GerardM55/TFG/Diseño mano/Archivos SLDPRT/falange proximal 4.SLDPRT

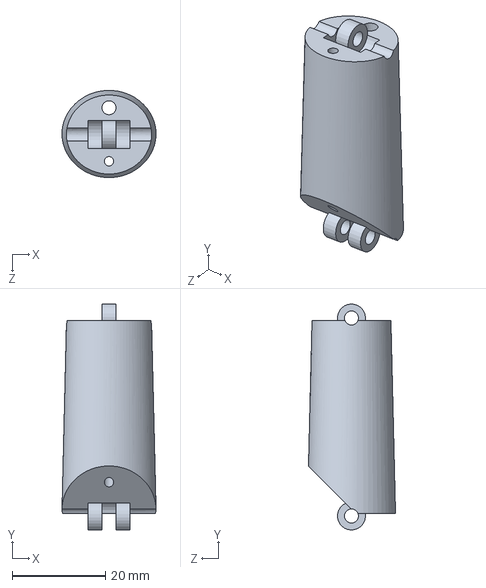
[picture p15: CAD file, 2025-07-18]
Diseño mano/Archivos SLDPRT/falange proximal 4.SLDPRT
20.2 x 48.4 x 18.6 mm
