GerardM55/TFG/Diseño mano/Archivos SLDPRT/falange proximal 3.SLDPRT

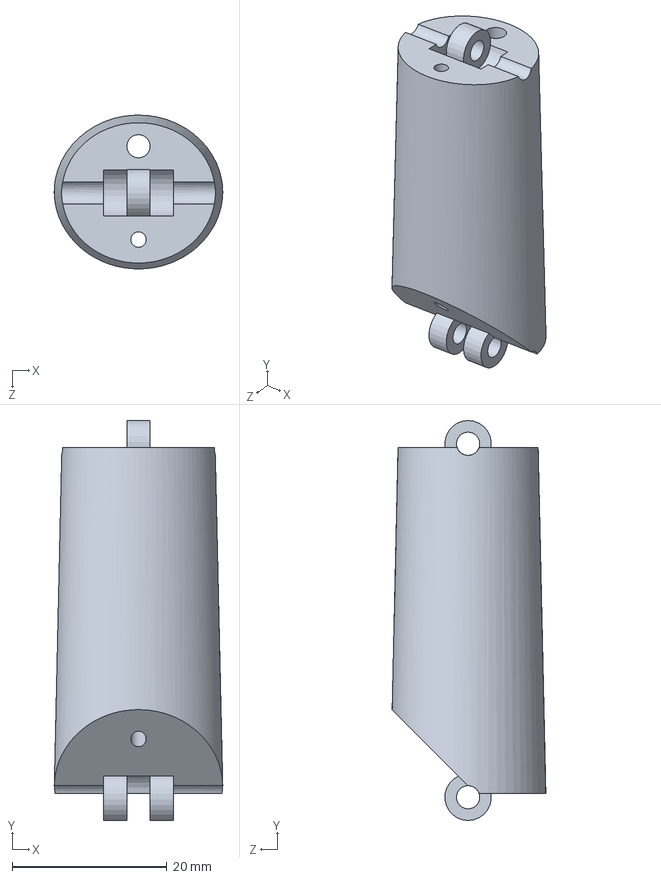
[picture p16: CAD file, 2025-07-18]
Diseño mano/Archivos SLDPRT/falange proximal 3.SLDPRT
21.8 x 51.6 x 19.9 mm
