GerardM55/TFG/Diseño mano/Archivos SLDPRT/falange proximal 2.SLDPRT

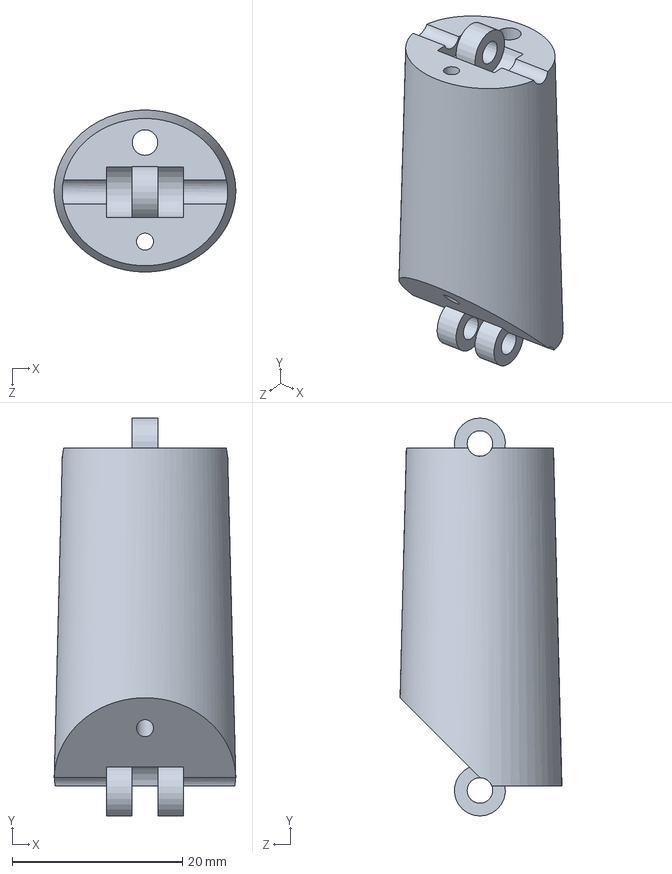
[picture p17: CAD file, 2025-07-18]
Diseño mano/Archivos SLDPRT/falange proximal 2.SLDPRT
21.3 x 46.8 x 19.0 mm
