GerardM55/TFG/Diseño mano/Archivos SLDPRT/pasador.SLDPRT

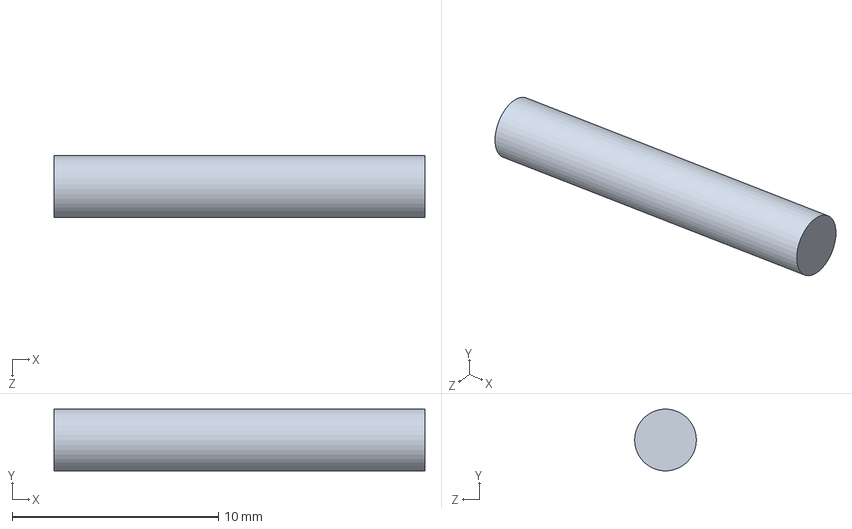
[picture p18: CAD file, 2025-07-18]
Diseño mano/Archivos SLDPRT/pasador.SLDPRT
18.0 x 2.99 x 3.00 mm
