GerardM55/TFG/Diseño mano/Archivos SLDPRT/falange proximal 1.SLDPRT

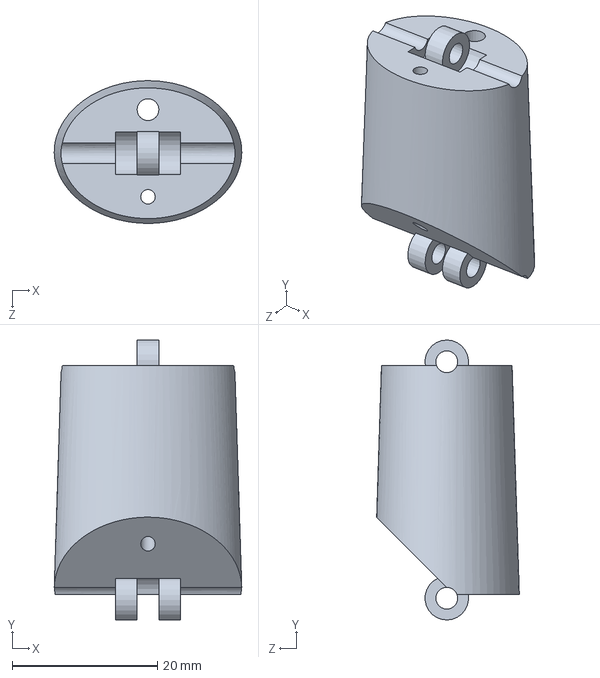
[picture p19: CAD file, 2025-07-18]
Diseño mano/Archivos SLDPRT/falange proximal 1.SLDPRT
25.8 x 38.6 x 19.7 mm
