GerardM55/TFG/Diseño mano/Archivos SLDPRT/servoHorn.SLDPRT

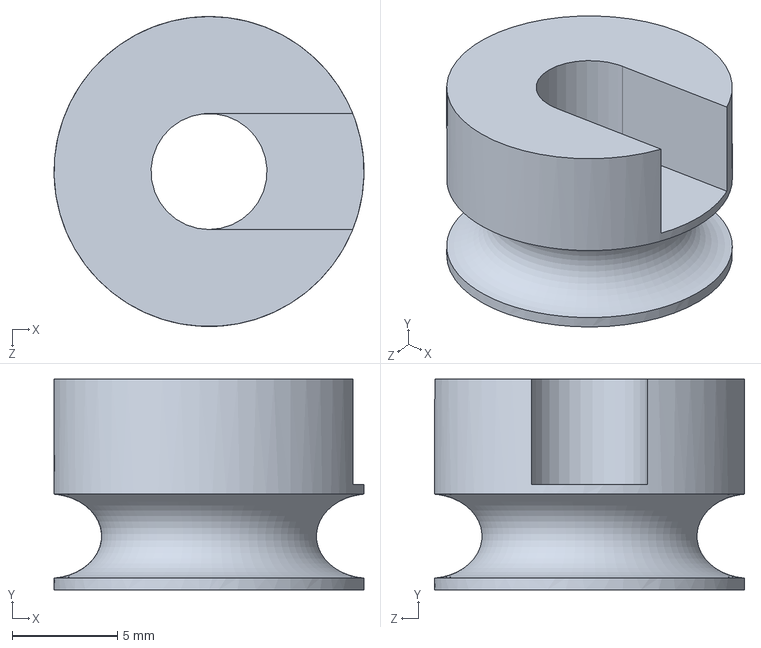
[picture p20: CAD file, 2025-07-18]
Diseño mano/Archivos SLDPRT/servoHorn.SLDPRT
14.7 x 10.0 x 14.7 mm
