GerardM55/TFG/Diseño mano/Archivos SLDPRT/falange proximal 3 sp.SLDPRT

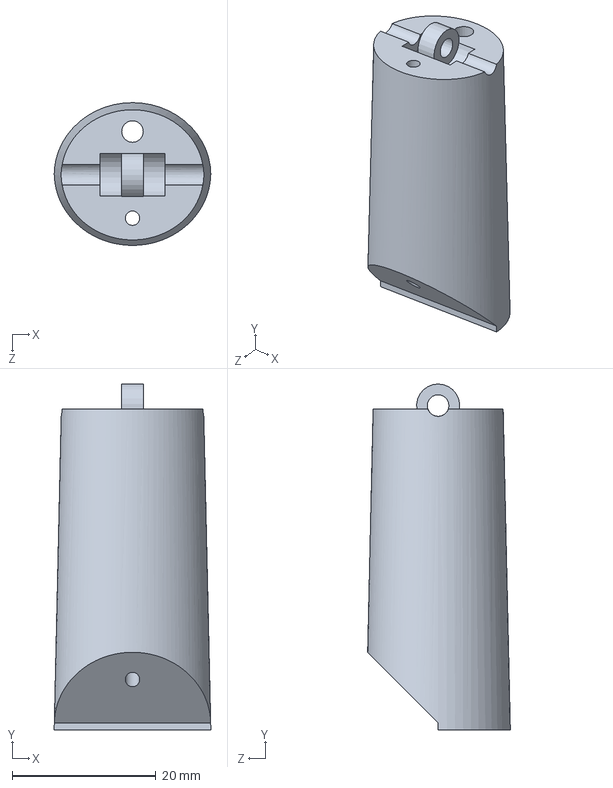
[picture p21: CAD file, 2025-07-18]
Diseño mano/Archivos SLDPRT/falange proximal 3 sp.SLDPRT
21.8 x 48.1 x 19.9 mm
