GerardM55/TFG/Diseño mano/Archivos SLDPRT/falange distal 2.SLDPRT

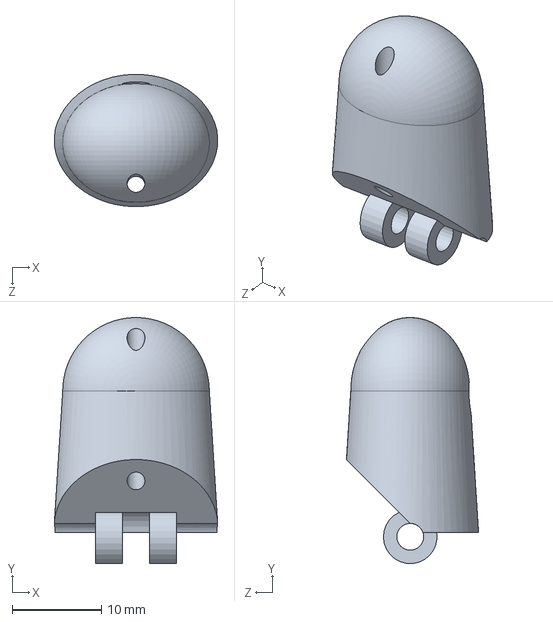
[picture p22: CAD file, 2025-07-18]
Diseño mano/Archivos SLDPRT/falange distal 2.SLDPRT
18.3 x 27.5 x 14.8 mm
