GerardM55/TFG/Diseño mano/Archivos SLDPRT/ajustadorSG90.SLDPRT

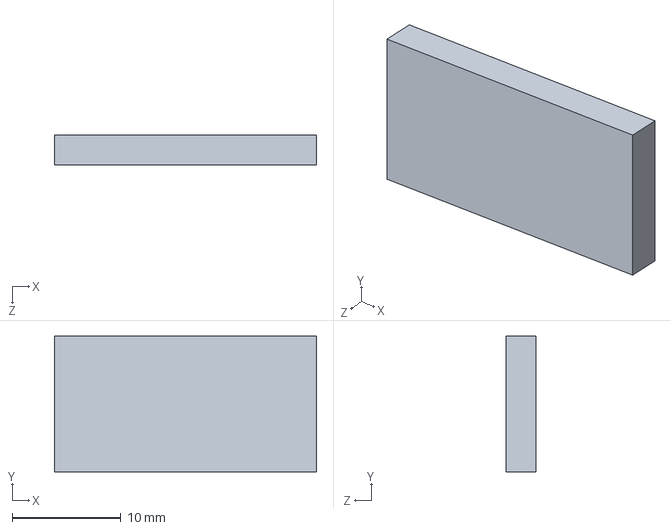
[picture p23: CAD file, 2025-07-18]
Diseño mano/Archivos SLDPRT/ajustadorSG90.SLDPRT
24.1 x 12.5 x 2.80 mm
