GerardM55/TFG/Diseño mano/Archivos SLDPRT/falange media 5.SLDPRT

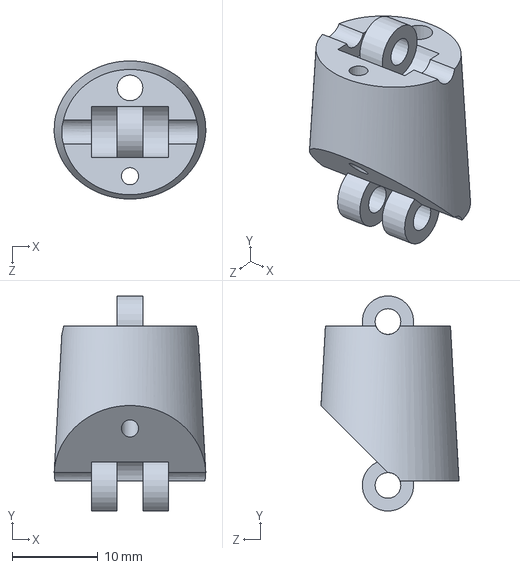
[picture p24: CAD file, 2025-07-18]
Diseño mano/Archivos SLDPRT/falange media 5.SLDPRT
17.7 x 25.1 x 16.1 mm
