GerardM55/TFG/Diseño mano/Archivos SLDPRT/mano.SLDPRT

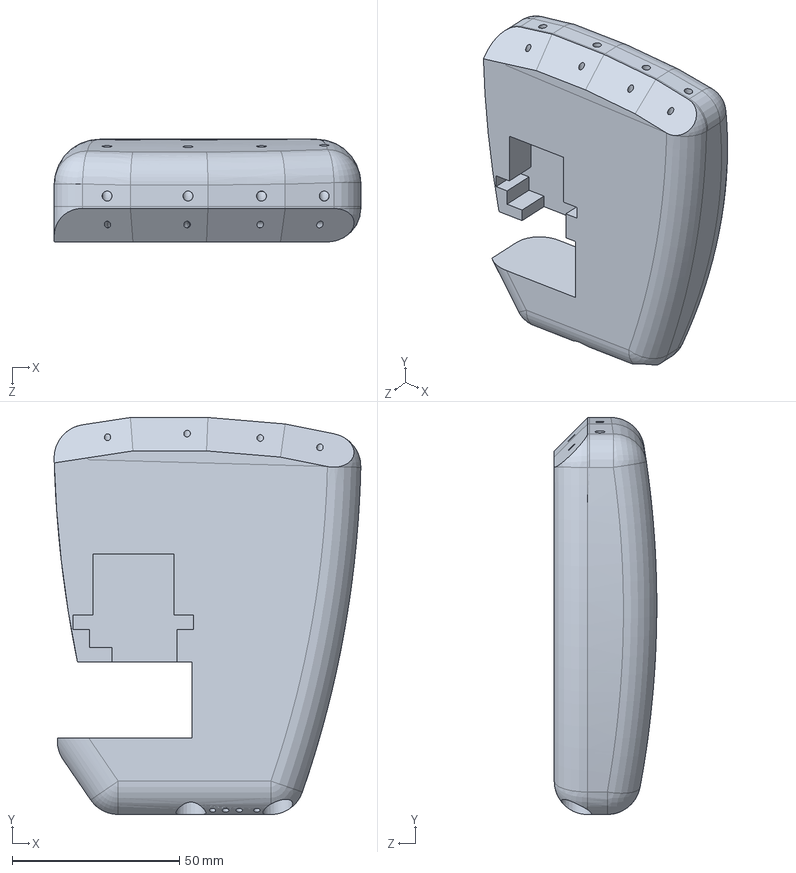
[picture p25: CAD file, 2025-07-18]
Diseño mano/Archivos SLDPRT/mano.SLDPRT
91.8 x 118.8 x 30.7 mm
