GerardM55/TFG/Diseño mano/Archivos SLDPRT/falange distal 3.SLDPRT

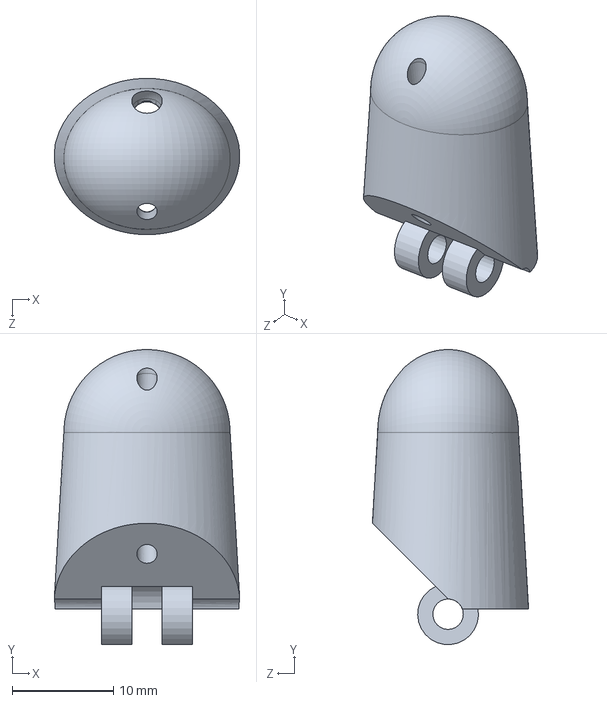
[picture p26: CAD file, 2025-07-18]
Diseño mano/Archivos SLDPRT/falange distal 3.SLDPRT
18.3 x 29.1 x 15.4 mm
