GerardM55/TFG/Diseño mano/Archivos SLDPRT/falange distal 1.SLDPRT

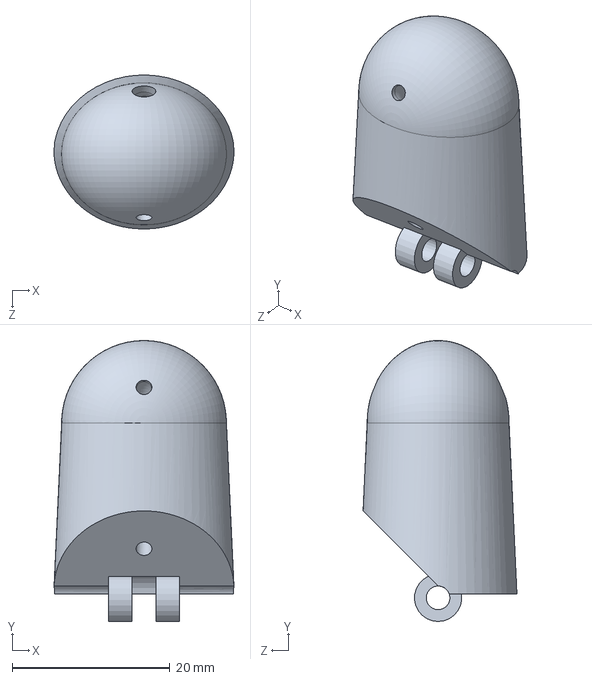
[picture p27: CAD file, 2025-07-18]
Diseño mano/Archivos SLDPRT/falange distal 1.SLDPRT
22.8 x 35.6 x 19.5 mm
