GerardM55/TFG/Diseño mano/Archivos SLDPRT/falange media 3.SLDPRT

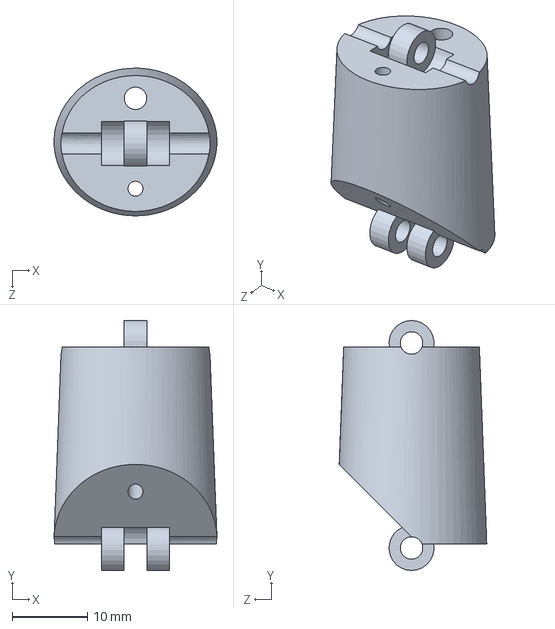
[picture p28: CAD file, 2025-07-18]
Diseño mano/Archivos SLDPRT/falange media 3.SLDPRT
21.7 x 33.3 x 19.7 mm
