GerardM55/TFG/Diseño mano/Archivos SLDPRT/falange proximal 2 sp.SLDPRT

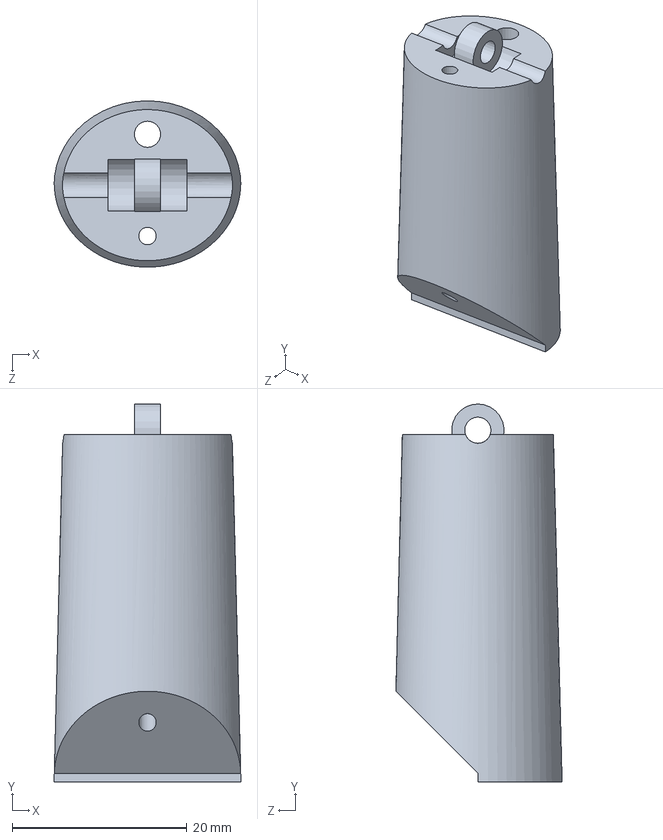
[picture p29: CAD file, 2025-07-18]
Diseño mano/Archivos SLDPRT/falange proximal 2 sp.SLDPRT
21.4 x 43.3 x 19.0 mm
