GerardM55/TFG/Diseño mano/Archivos SLDPRT/falange distal 4.SLDPRT

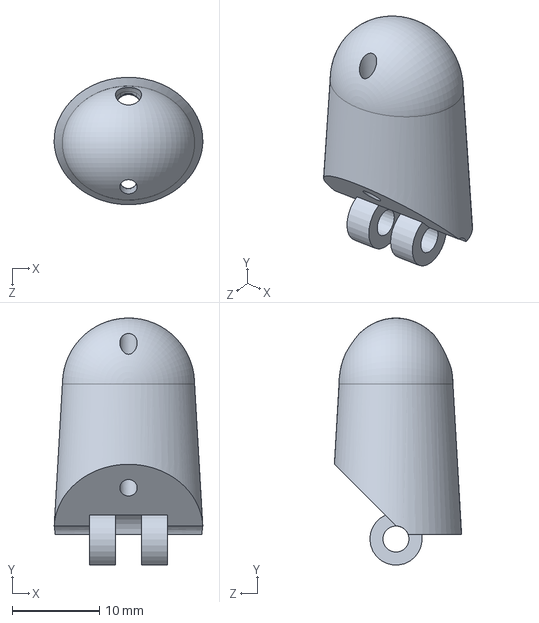
[picture p30: CAD file, 2025-07-18]
Diseño mano/Archivos SLDPRT/falange distal 4.SLDPRT
17.1 x 28.4 x 14.6 mm
